svenpetersen1965/Commodore-Keyboard-Tester/Rev. 0/pictures/screenshot.png

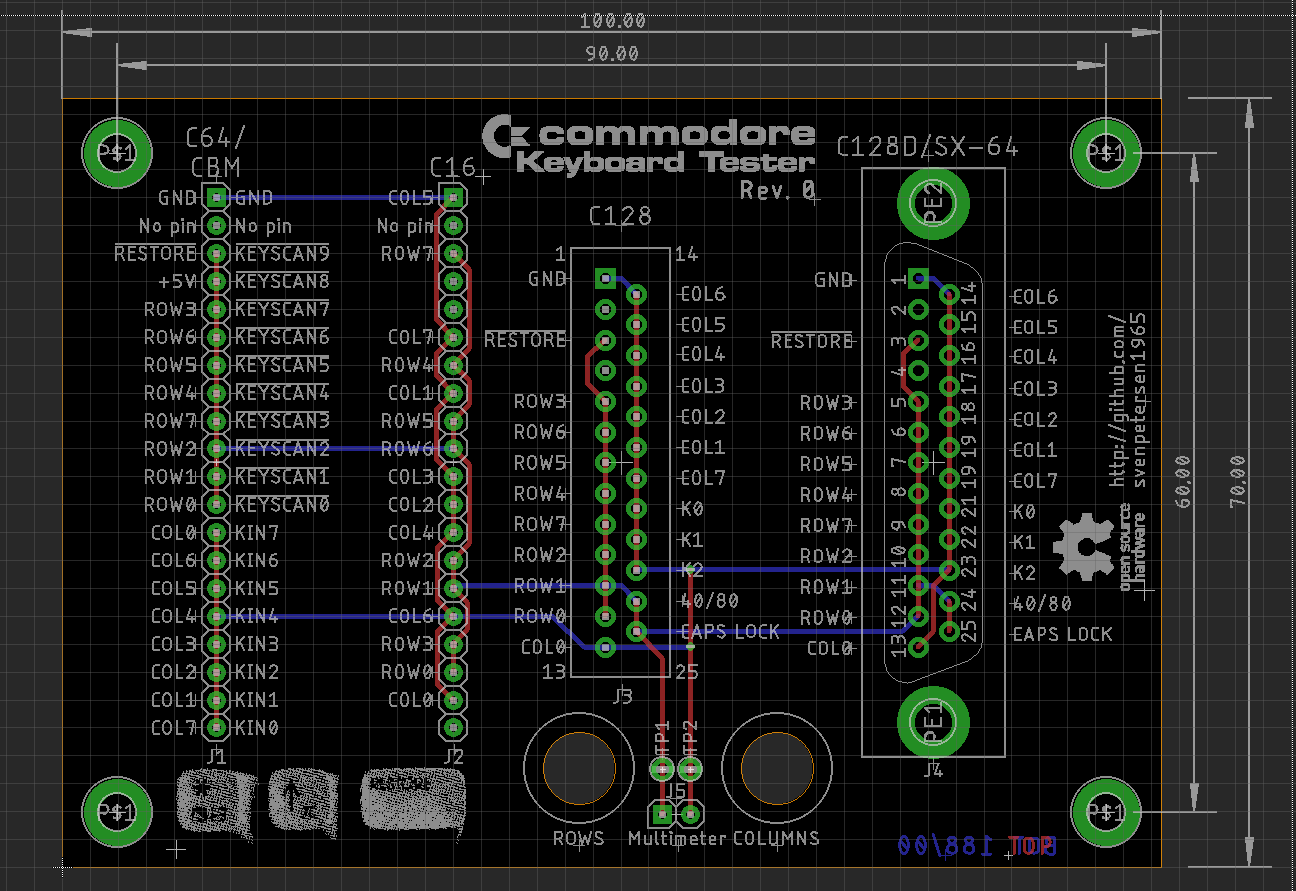
Rev. 0/pictures/screenshot.png
